autonomous-ai/autonomous-computer/2x-6000/photos/gallery/gpu-card.webp

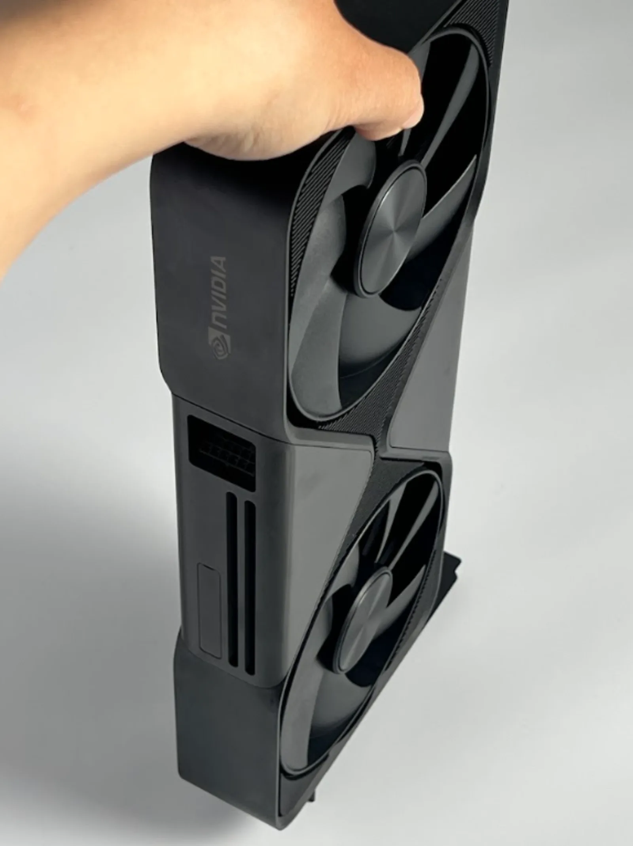
2x-6000/photos/gallery/gpu-card.webp
